Aldrome/Compact-Keyboard/Compact_Piano/Metronome.h

#ifndef METRONOME_H
#define METRONOME_H

#include <IntervalTimer.h>
#include <Arduino.h>

enum MetronomeState { METRONOME_RUNNING, METRONOME_STOPPED };

struct SongMetronomeData {
     int bpm;
     int offsetMillis;
};

class AudioSynthSimpleDrum;

class Metronome {
public:
     // Constructor might take audio components or timer references
     Metronome(AudioSynthSimpleDrum* drumSynth);

     void begin();
     
     void setBPM(int bpm);
     int getBPM() const { return currentBPM; }

     void setOffset(int offsetMillis); 
     int getOffset() const { return offsetMillis; }

     void start();
     void stop();

     void syncStart();
     void syncStop();
     
     MetronomeState getState() const { return state; }

     void loadSongInfo(const SongMetronomeData& data);

     static void metronomeTickHandler();

private:
     AudioSynthSimpleDrum* tickSynth;

     MetronomeState state = METRONOME_STOPPED;
     
     int currentBPM = 120;
     int offsetMillis = 0;

     IntervalTimer metronomeTimer;
     
     void tick();

     static Metronome* instance;

     bool engineRunning = false;
     bool musicEngineRunning = false;
     bool isFirstBeat = true;
     elapsedMillis tickTimer;
     unsigned long usInterval = 0;
};

#endif
